whowechina/densha_pico/PCB/Prototype/3dmodels/SKSTAAE010.stp

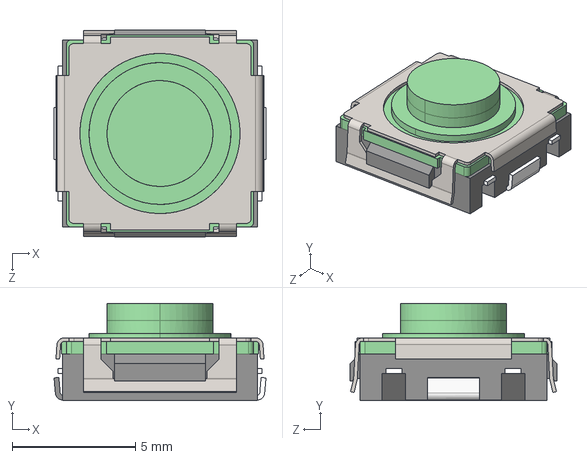
[picture p15: CAD file, 2026-03-25]
PCB/Prototype/3dmodels/SKSTAAE010.stp
8.61 x 3.95 x 8.40 mm
