whowechina/densha_pico/PCB/Prototype/3dmodels/WS2812-2020.STEP

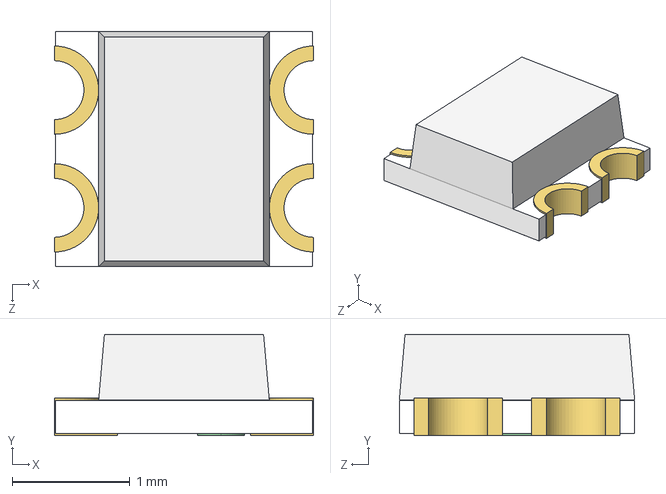
[picture p16: CAD file, 2026-03-25]
PCB/Prototype/3dmodels/WS2812-2020.STEP
2.20 x 0.86 x 2.00 mm
