whowechina/densha_pico/PCB/Prototype/3dmodels/User Library-WS2812-2020.step

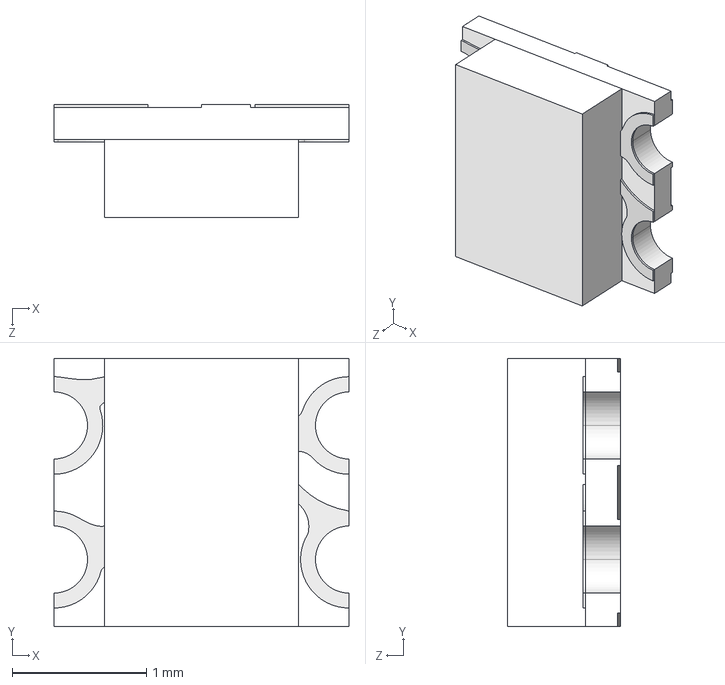
[picture p17: CAD file, 2026-03-25]
PCB/Prototype/3dmodels/User Library-WS2812-2020.step
2.20 x 2.00 x 0.84 mm
