whowechina/densha_pico/PCB/Prototype/3dmodels/User Library-PTS645SL95SMTR92-LFS.STEP

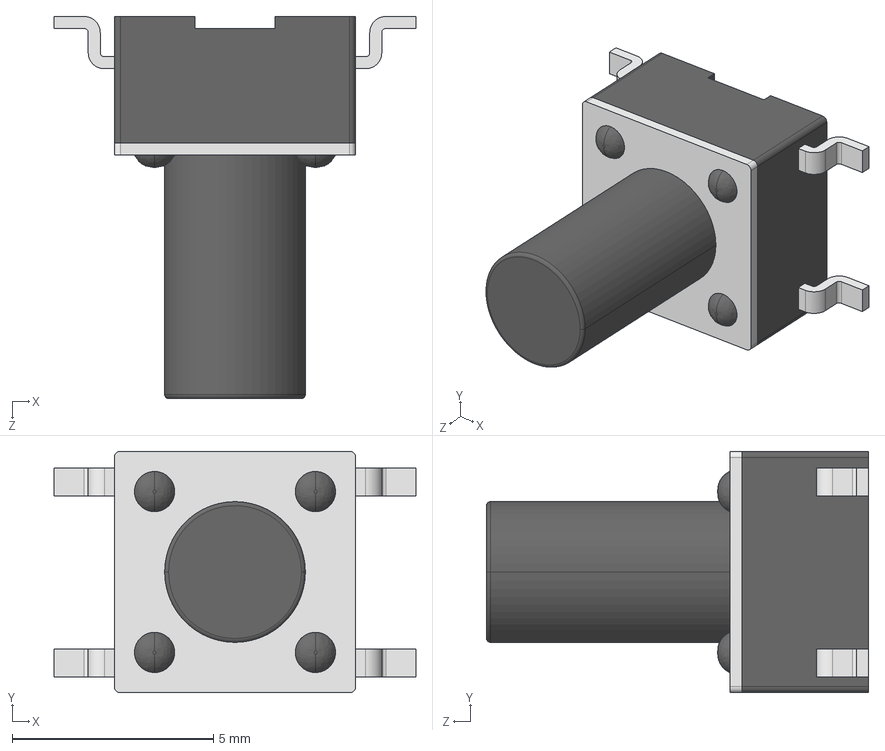
[picture p18: CAD file, 2026-03-25]
PCB/Prototype/3dmodels/User Library-PTS645SL95SMTR92-LFS.STEP
9.00 x 6.00 x 9.50 mm
