whowechina/densha_pico/PCB/Prototype/3dmodels/User Library-RGB1204.STEP

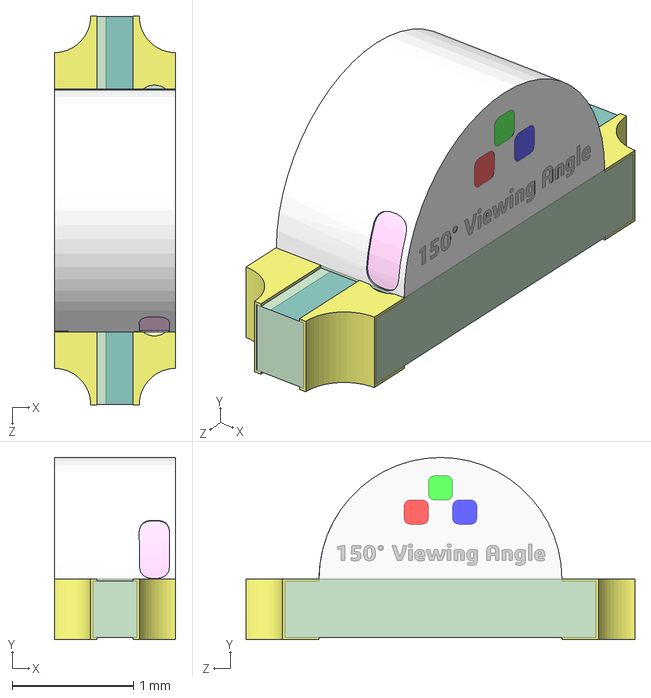
[picture p19: CAD file, 2026-03-25]
PCB/Prototype/3dmodels/User Library-RGB1204.STEP
1.00 x 1.50 x 3.20 mm
