whowechina/densha_pico/PCB/Prototype/3dmodels/FPC0.5MM10P.stp

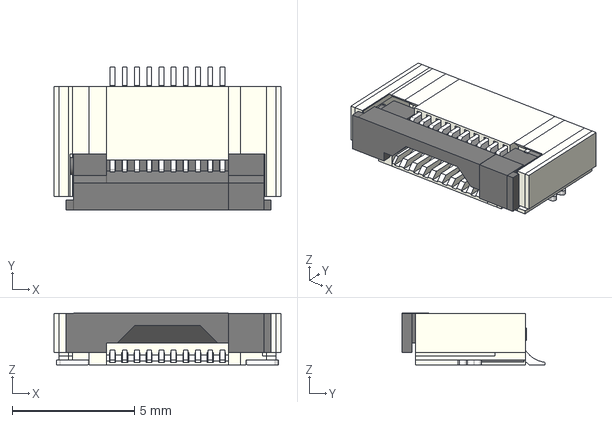
[picture p20: CAD file, 2026-03-25]
PCB/Prototype/3dmodels/FPC0.5MM10P.stp
9.30 x 5.85 x 2.11 mm
