whowechina/densha_pico/PCB/Prototype/3dmodels/WS2812-0807.STEP

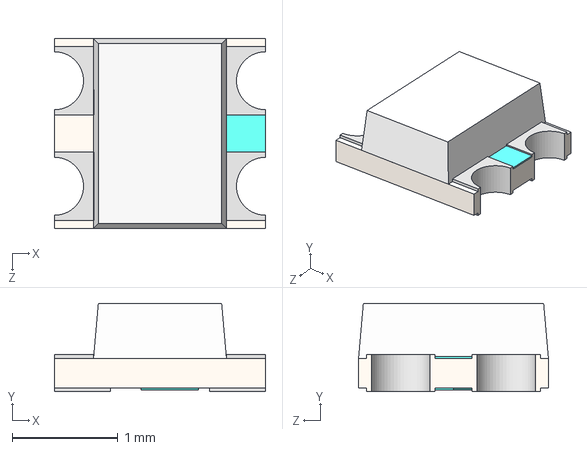
[picture p21: CAD file, 2026-03-25]
PCB/Prototype/3dmodels/WS2812-0807.STEP
2.00 x 0.835 x 1.80 mm
