whowechina/densha_pico/PCB/Prototype/3dmodels/SKRRABE010.stp

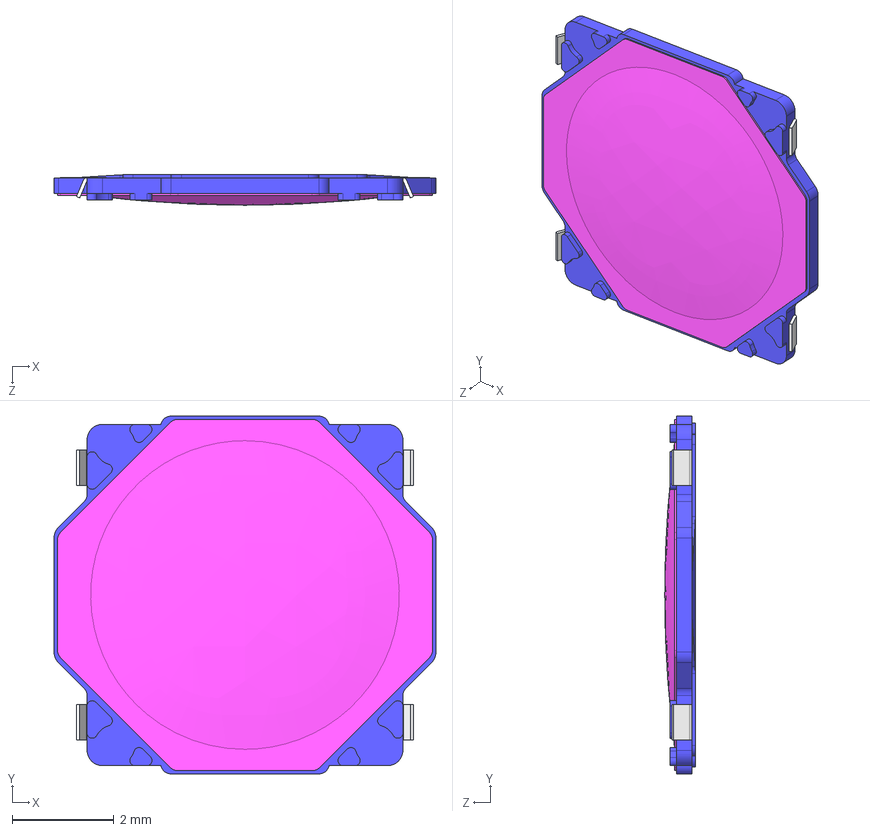
[picture p22: CAD file, 2026-03-25]
PCB/Prototype/3dmodels/SKRRABE010.stp
7.50 x 7.03 x 0.6 mm
