whowechina/densha_pico/firmware/src/c51_demo.c

/********************金逸晨**************************
*****************279VJ-C10-01 TFT   模块 2.79寸 8P SPI TFT FOR FOR AT89S52/STC12*************
*****AT89S52驱动**************************需设置引脚为推挽模式
***** P20----SCL   P21-----SDA			P22-----RST    P23-----DC    P24-----CS  P25-----BL
*********ST7789 控制器，需设置bl为推挽模式
默认数据格式位RGB565
***** BY:GU 


***********************************************/
#include "reg51.h"
#define LCD_DIS_CHINA_ROT  0


#define set_0   0x01
#define set_1   0x02
#define set_2   0x04
#define set_3   0x08    
#define set_4   0x10
#define set_5   0x20
#define set_6   0x40
#define set_7   0x80

#define clr_0   0xFE
#define clr_1   0xFD
#define clr_2   0xFB
#define clr_3   0xF7    
#define clr_4   0xEF
#define clr_5   0xDF
#define clr_6   0xBF
#define clr_7   0x7F


///////stc   IO   模式寄存器
sfr P1M1 = 0x91;    //PxM1.n,PxM0.n     =00--->Standard,    01--->push-pull
sfr P1M0 = 0x92;    //                  =10--->pure input,  11--->open drain
sfr P0M1 = 0x93;
sfr P0M0 = 0x94;
sfr P2M1 = 0x95;
sfr P2M0 = 0x96;
sfr P3M1 = 0xB1;
sfr P3M0 = 0xB2;
sfr P4M1 = 0xB3;
sfr P4M0 = 0xB4;
sfr P5M1 = 0xC9;
sfr P5M0 = 0xCA;
sfr P6M1 = 0xCB;
sfr P6M0 = 0xCC;
sfr P7M1 = 0xE1;
sfr P7M0 = 0xE2;

/**********引脚分配，连接LCD屏，更具实际情况修改*********/
     
#define TFT_SCK_0   	P2 &=clr_0    // 设置CS接口到P20
#define TFT_SCK_1   	P2|=set_0
#define TFT_SDA_0   	P2 &=clr_1      // 设置DC接口到P21
#define TFT_SDA_1   	P2|=set_1
#define TFT_RST_0  	P2 &=clr_2      // 设置WR接口到P22   清零
#define TFT_RST_1  	P2|=set_2       //置位
#define TFT_DC_0  	P2 &=clr_3      // 设置RD接口到P23
#define TFT_DC_1  	P2|=set_3
#define TFT_CS_0  	P2 &=clr_4       // 设置RST接口到P24
#define TFT_CS_1 	P2|=set_4
#define TFT_BL_0  	P2 &=clr_5      // 设置RST接口到P25
#define TFT_BL_1  	P2|=set_5

#define DIS_DIR  0
#define     RED          0XF800	  //红色
#define     GREEN        0X07E0	  //绿色
#define     BLUE         0X001F	  //蓝色
#define     WHITE        0XFFFF	  //白色
#define     BLACK        0X0000  //黑色

#define TFT_COLUMN_NUMBER 142
#define TFT_LINE_NUMBER 428
#define TFT_COLUMN_OFFSET 12

#define PIC_NUM 28800			//图片数据大小
unsigned char  *point;
code unsigned char  chines_word[   ][32]=   //汉字码
{
0x00,0x00,0xE4,0x3F,0x28,0x20,0x28,0x25,0x81,0x08,0x42,0x10,0x02,0x02,0x08,0x02,
0xE8,0x3F,0x04,0x02,0x07,0x07,0x84,0x0A,0x44,0x12,0x34,0x62,0x04,0x02,0x00,0x02,/*"深",0*/

0x88,0x20,0x88,0x24,0x88,0x24,0x88,0x24,0x88,0x24,0xBF,0x24,0x88,0x24,0x88,0x24,
0x88,0x24,0x88,0x24,0x88,0x24,0xB8,0x24,0x87,0x24,0x42,0x24,0x40,0x20,0x20,0x20,/*"圳",1*/

0x80,0x00,0x80,0x00,0x40,0x01,0x20,0x02,0x10,0x04,0x08,0x08,0xF4,0x17,0x83,0x60,
0x80,0x00,0xFC,0x1F,0x80,0x00,0x88,0x08,0x90,0x08,0x90,0x04,0xFF,0x7F,0x00,0x00,/*"金",2*/

0x80,0x00,0x82,0x00,0x84,0x0F,0x44,0x08,0x20,0x04,0xF0,0x3F,0x27,0x22,0x24,0x22,
0xE4,0x3F,0x04,0x05,0x84,0x0C,0x84,0x54,0x44,0x44,0x24,0x78,0x0A,0x00,0xF1,0x7F,/*"逸",3*/

0xF8,0x0F,0x08,0x08,0xF8,0x0F,0x08,0x08,0xF8,0x0F,0x00,0x00,0xFC,0x3F,0x04,0x00,
0xF4,0x1F,0x04,0x00,0xFC,0x7F,0x94,0x10,0x14,0x09,0x12,0x06,0x52,0x18,0x31,0x60,/*"晨",4*/

0x80,0x00,0x80,0x00,0x80,0x00,0xFC,0x1F,0x84,0x10,0x84,0x10,0x84,0x10,0xFC,0x1F,
0x84,0x10,0x84,0x10,0x84,0x10,0xFC,0x1F,0x84,0x50,0x80,0x40,0x80,0x40,0x00,0x7F,/*"电",5*/

0x00,0x00,0xFE,0x1F,0x00,0x08,0x00,0x04,0x00,0x02,0x80,0x01,0x80,0x00,0xFF,0x7F,
0x80,0x00,0x80,0x00,0x80,0x00,0x80,0x00,0x80,0x00,0x80,0x00,0xA0,0x00,0x40,0x00,/*"子",6*/
};


code unsigned char  picture_tab[PIC_NUM]={
/*------------------------------------------------------------------------------
120*120   16位彩色图片，取模方式，水平取模，高位在前
------------------------------------------------------------------------------*/
0X8D,0X62,0X8D,0X42,0X85,0X01,0X7C,0XC1,0X74,0X80,0X6C,0X60,0X6C,0X60,0X6C,0X80,
0X74,0XA1,0X7C,0XC1,0X85,0X01,0X85,0X42,0X8D,0X62,0X95,0X82,0X95,0XA2,0X9D,0XC2,
0X9E,0X02,0XA6,0X42,0XAE,0X83,0XB6,0XC4,0XC7,0X26,0XC7,0X47,0XCF,0X47,0XCF,0X68,
0XD7,0X89,0XD7,0X89,0XDF,0XAB,0XE7,0XCC,0XE7,0XCD,0XE7,0XCD,0XE7,0XCD,0XE7,0XCE,
0XE7,0XCD,0XE7,0XCD,0XE7,0XCD,0XE7,0XCD,0XEF,0XCD,0XEF,0XCD,0XEF,0XCD,0XEF,0XCD,
0XE7,0XCC,0XE7,0XCC,0XE7,0XCB,0XDF,0XCB,0XDF,0XAA,0XD7,0XA9,0XD7,0X88,0XD7,0X88,
0XD7,0X87,0XD7,0X67,0XCF,0X66,0XC7,0X26,0XC7,0X05,0XBE,0XE5,0XB6,0XC5,0XB6,0XC5,
0XAE,0X84,0XA6,0X64,0XA6,0X24,0X9D,0XE3,0X95,0XA3,0X95,0X83,0X8D,0X42,0X8D,0X22,
0X85,0X22,0X85,0X01,0X7C,0XC1,0X74,0XC1,0X74,0XA1,0X74,0X81,0X6C,0X40,0X64,0X20,
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
0X39,0XC4,0X39,0XA4,0X18,0XC0,0X29,0X22,0X29,0X22,0X18,0XE2,0X08,0X40,0X39,0XC5,
0X31,0X84,0X31,0XA4,0X08,0X60,0X29,0X63,0X21,0X43,0X21,0X02,0X19,0X01,0X10,0X80,
0X29,0X62,0X31,0X63,0X29,0X44,0X20,0XE3,0X20,0XE2,0X29,0X02,0X21,0X02,0X21,0X01,
0X29,0X42,0X10,0X80,0X4A,0X46,0X63,0X09,0X18,0XC0,0X29,0X63,0X08,0X60,0X42,0X25,
0X31,0X83,0X29,0X62,0X19,0X00,0X63,0X49,0X42,0X25,0X29,0X41,0X5A,0XC7,0X29,0X41,
0X63,0X08,0X5A,0XE7,0X42,0X24,0X29,0X62,0X29,0X42,0X4A,0X46,0X18,0XC0,0X20,0XE0,
0X39,0XC4,0X29,0X21,0X29,0X21,0X29,0X01,0X41,0XC4,0X8C,0X0D,0X94,0X0D,0XD6,0X36,
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
