whowechina/densha_pico/firmware/src/gui.h

/*
 * GUI on a Touch Display (NV3007 + CST816)
 * WHowe <github.com/whowechina>
 * 
 */

#ifndef GUI_H
#define GUI_H

#include <stdint.h>
#include <stdbool.h>

void gui_init();
void gui_level(uint8_t level);
void gui_loop();

#endif
